Rohan-Gupta99/PrakritiNetX/assets/screenshots/mobile_app_pngs/WhatsApp Image 2026-09-10 at 23.43.37.jpeg

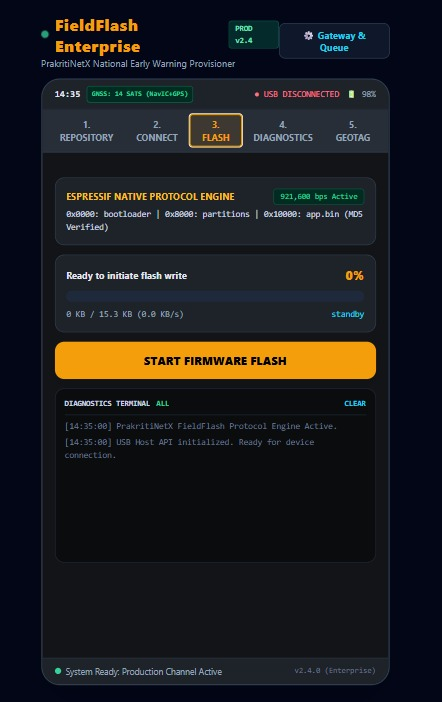
assets/screenshots/mobile_app_pngs/WhatsApp Image 2026-09-10 at 23.43.37.jpeg
