Rohan-Gupta99/PrakritiNetX/assets/screenshots/power_system_diagram.png

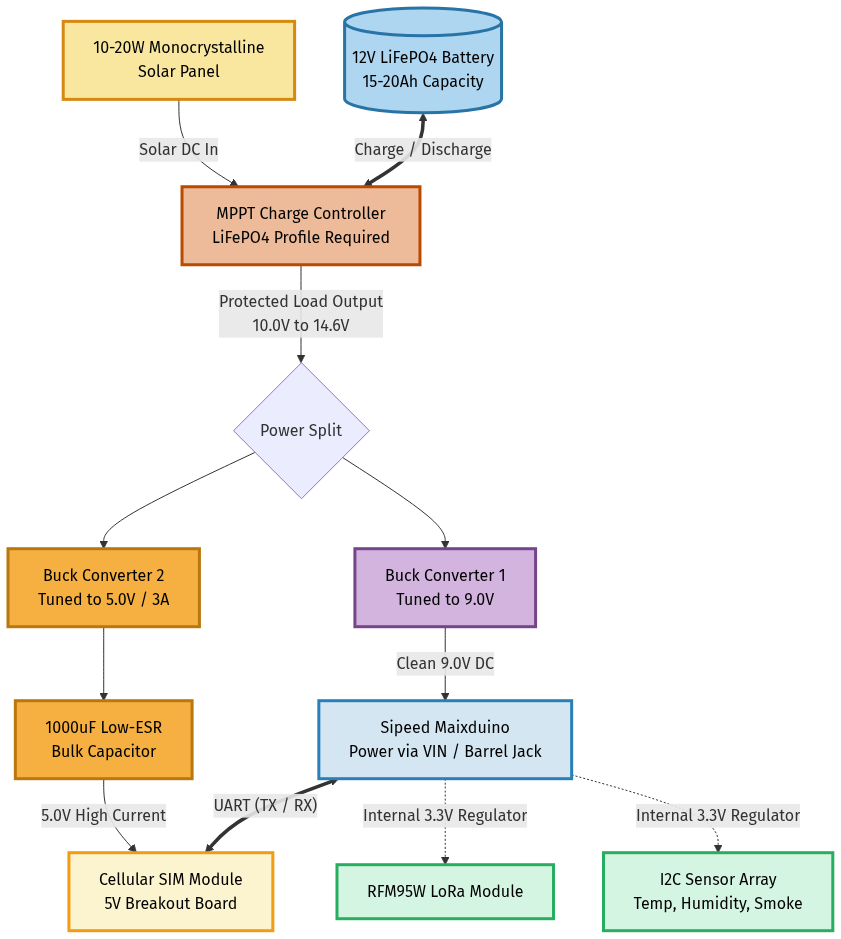
assets/screenshots/power_system_diagram.png
