Rohan-Gupta99/PrakritiNetX/Hardware/Sensor_board/Sensor_board.kicad_pcb

## KiCad design hardware/kicad/boards/01_alu/alu-32b.kicad_pcb

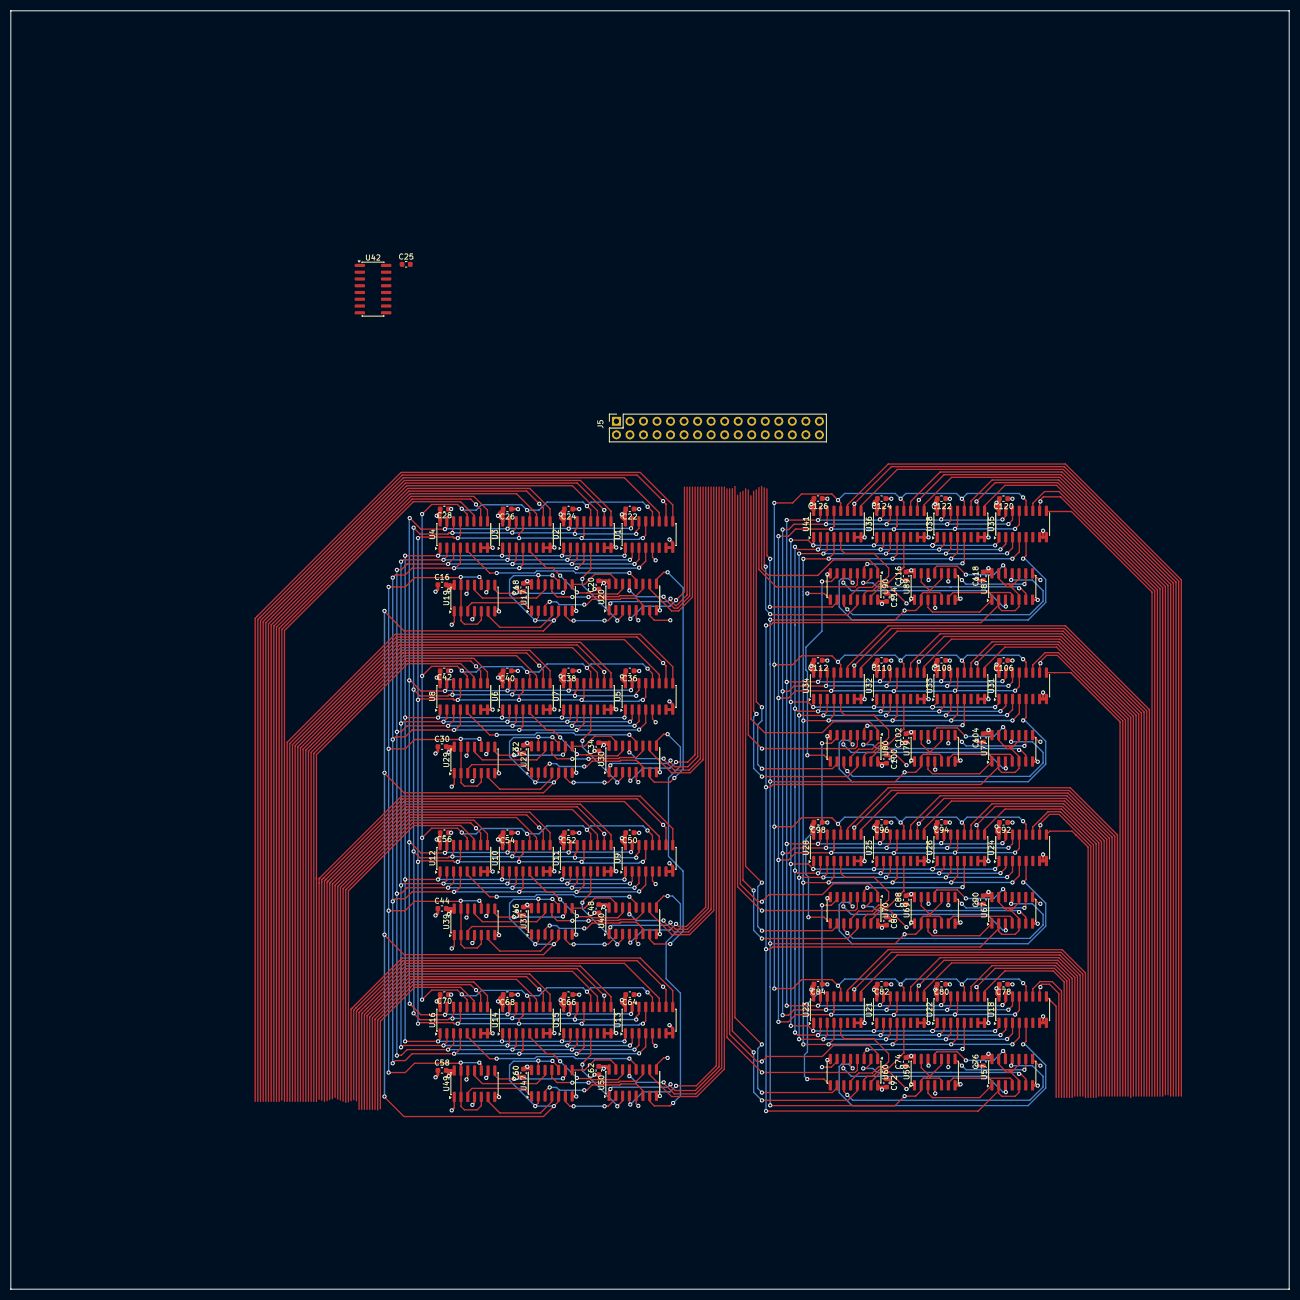
[picture p24: board alu-32b.kicad_pcb from above]

Board: 4 copper layers, 240.0 x 240.0 mm, 115 parts (0 on the bottom side), 179 nets.

Parts:
C16, C18, C20, C22, C24, C25, C26, C28, C30, C32, C34, C36, C38, C40, C42, C44, C46, C48, C50, C52, C54, C56, C58, C60, C62, C64, C66, C68, C70, C72, C74, C76, C78, C80, C82, C84, C86, C88, C90, C92, C94, C96, C98, C100, C102, C104, C106, C108, C110, C112, C114, C116, C118, C120, C122, C124, C126: 100nF; C_0603_1608Metric
J5: Conn_02x16_Counter_Clockwise; PinSocket_2x16_P2.54mm_Vertical
U1, U2, U3, U4, U5, U6, U7, U8, U9, U10, U11, U12, U13, U14, U15, U16, U18, U21, U22, U23, U24, U25, U26, U28, U31, U32, U33, U34, U35, U36, U38, U41, U42: 74ACT151; SOIC-16_3.9x9.9mm_P1.27mm
U17, U27, U37, U47, U57, U67, U77, U87: 74HC86; SOIC-14_3.9x8.7mm_P1.27mm
U19, U29, U39, U49, U59, U69, U79, U89: 74HC00; SOIC-14_3.9x8.7mm_P1.27mm
U20, U30, U40, U50, U60, U70, U80, U90: 74ACT283; SOIC-16_3.9x9.9mm_P1.27mm

Connections:
/alu-4b-0/log0: U1.5 (Z), U20.5 (A1)
/alu-4b-0/log1: U2.5 (Z), U20.3 (A2)
/alu-4b-0/log2: U3.5 (Z), U20.14 (A3)
/alu-4b-0/log3: U4.5 (Z), U20.12 (A4)
/alu-4b-0/sB0: U17.3, U20.6 (B1)
/alu-4b-0/sB1: U17.6, U20.2 (B2)
/alu-4b-0/sB2: U17.8, U20.15 (B3)
/alu-4b-0/sB3: U17.11, U20.11 (B4)
/alu-4b-1/log0: U5.5 (Z), U30.5 (A1)
/alu-4b-1/log1: U7.5 (Z), U30.3 (A2)
/alu-4b-1/log2: U6.5 (Z), U30.14 (A3)
/alu-4b-1/log3: U8.5 (Z), U30.12 (A4)
/alu-4b-1/sB0: U27.3, U30.6 (B1)
/alu-4b-1/sB1: U27.6, U30.2 (B2)
/alu-4b-1/sB2: U27.8, U30.15 (B3)
/alu-4b-1/sB3: U27.11, U30.11 (B4)
/alu-4b-2/log0: U9.5 (Z), U40.5 (A1)
/alu-4b-2/log1: U11.5 (Z), U40.3 (A2)
/alu-4b-2/log2: U10.5 (Z), U40.14 (A3)
/alu-4b-2/log3: U12.5 (Z), U40.12 (A4)
/alu-4b-2/sB0: U37.3, U40.6 (B1)
/alu-4b-2/sB1: U37.6, U40.2 (B2)
/alu-4b-2/sB2: U37.8, U40.15 (B3)
/alu-4b-2/sB3: U37.11, U40.11 (B4)
/alu-4b-3/log0: U13.5 (Z), U50.5 (A1)
/alu-4b-3/log1: U15.5 (Z), U50.3 (A2)
/alu-4b-3/log2: U14.5 (Z), U50.14 (A3)
/alu-4b-3/log3: U16.5 (Z), U50.12 (A4)
/alu-4b-3/sB0: U47.3, U50.6 (B1)
/alu-4b-3/sB1: U47.6, U50.2 (B2)
/alu-4b-3/sB2: U47.8, U50.15 (B3)
/alu-4b-3/sB3: U47.11, U50.11 (B4)
/alu-4b-4/log0: U18.5 (Z), U60.5 (A1)
/alu-4b-4/log1: U22.5 (Z), U60.3 (A2)
/alu-4b-4/log2: U21.5 (Z), U60.14 (A3)
/alu-4b-4/log3: U23.5 (Z), U60.12 (A4)
/alu-4b-4/sB0: U57.3, U60.6 (B1)
/alu-4b-4/sB1: U57.6, U60.2 (B2)
/alu-4b-4/sB2: U57.8, U60.15 (B3)
/alu-4b-4/sB3: U57.11, U60.11 (B4)
/alu-4b-5/log0: U24.5 (Z), U70.5 (A1)
/alu-4b-5/log1: U26.5 (Z), U70.3 (A2)
/alu-4b-5/log2: U25.5 (Z), U70.14 (A3)
/alu-4b-5/log3: U28.5 (Z), U70.12 (A4)
/alu-4b-5/sB0: U67.3, U70.6 (B1)
/alu-4b-5/sB1: U67.6, U70.2 (B2)
/alu-4b-5/sB2: U67.8, U70.15 (B3)
/alu-4b-5/sB3: U67.11, U70.11 (B4)
/alu-4b-6/log0: U31.5 (Z), U80.5 (A1)
/alu-4b-6/log1: U33.5 (Z), U80.3 (A2)
/alu-4b-6/log2: U32.5 (Z), U80.14 (A3)
/alu-4b-6/log3: U34.5 (Z), U80.12 (A4)
/alu-4b-6/sB0: U77.3, U80.6 (B1)
/alu-4b-6/sB1: U77.6, U80.2 (B2)
/alu-4b-6/sB2: U77.8, U80.15 (B3)
/alu-4b-6/sB3: U77.11, U80.11 (B4)
/alu-4b-7/log0: U35.5 (Z), U90.5 (A1)
/alu-4b-7/log1: U38.5 (Z), U90.3 (A2)
/alu-4b-7/log2: U36.5 (Z), U90.14 (A3)
/alu-4b-7/sB0: U87.3, U90.6 (B1)
/alu-4b-7/sB1: U87.6, U90.2 (B2)
/alu-4b-7/sB2: U87.8, U90.15 (B3)
/cout0: U20.9 (C4), U30.7 (C0)
/cout1: U30.9 (C4), U40.7 (C0)
/cout2: U40.9 (C4), U50.7 (C0)
/cout3: U50.9 (C4), U60.7 (C0)
/cout4: U60.9 (C4), U70.7 (C0)
/cout5: U70.9 (C4), U80.7 (C0)
/cout6: U80.9 (C4), U90.7 (C0)
AEFF31: U41.5 (Z), U90.12 (A4)
ALU-OPCODE0: U1.4 (I0), U2.4 (I0), U3.4 (I0), U4.4 (I0), U5.4 (I0), U6.4 (I0), U7.4 (I0), U8.4 (I0), U9.4 (I0), U10.4 (I0), U11.4 (I0), U12.4 (I0), U13.4 (I0), U14.4 (I0), U15.4 (I0), U16.4 (I0), U18.4 (I0), U21.4 (I0), U22.4 (I0), U23.4 (I0), U24.4 (I0), U25.4 (I0), U26.4 (I0), U28.4 (I0), U31.4 (I0), U32.4 (I0), U33.4 (I0), U34.4 (I0), U35.4 (I0), U36.4 (I0), U38.4 (I0), U41.4 (I0)
ALU-OPCODE1: U1.3 (I1), U2.3 (I1), U3.3 (I1), U4.3 (I1), U5.3 (I1), U6.3 (I1), U7.3 (I1), U8.3 (I1), U9.3 (I1), U10.3 (I1), U11.3 (I1), U12.3 (I1), U13.3 (I1), U14.3 (I1), U15.3 (I1), U16.3 (I1), U18.3 (I1), U21.3 (I1), U22.3 (I1), U23.3 (I1), U24.3 (I1), U25.3 (I1), U26.3 (I1), U28.3 (I1), U31.3 (I1), U32.3 (I1), U33.3 (I1), U34.3 (I1), U35.3 (I1), U36.3 (I1), U38.3 (I1), U41.3 (I1)
ALU-OPCODE2: U1.2 (I2), U2.2 (I2), U3.2 (I2), U4.2 (I2), U5.2 (I2), U6.2 (I2), U7.2 (I2), U8.2 (I2), U9.2 (I2), U10.2 (I2), U11.2 (I2), U12.2 (I2), U13.2 (I2), U14.2 (I2), U15.2 (I2), U16.2 (I2), U18.2 (I2), U21.2 (I2), U22.2 (I2), U23.2 (I2), U24.2 (I2), U25.2 (I2), U26.2 (I2), U28.2 (I2), U31.2 (I2), U32.2 (I2), U33.2 (I2), U34.2 (I2), U35.2 (I2), U36.2 (I2), U38.2 (I2), U41.2 (I2)
ALU-OPCODE3: U1.1 (I3), U2.1 (I3), U3.1 (I3), U4.1 (I3), U5.1 (I3), U6.1 (I3), U7.1 (I3), U8.1 (I3), U9.1 (I3), U10.1 (I3), U11.1 (I3), U12.1 (I3), U13.1 (I3), U14.1 (I3), U15.1 (I3), U16.1 (I3), U18.1 (I3), U21.1 (I3), U22.1 (I3), U23.1 (I3), U24.1 (I3), U25.1 (I3), U26.1 (I3), U28.1 (I3), U31.1 (I3), U32.1 (I3), U33.1 (I3), U34.1 (I3), U35.1 (I3), U36.1 (I3), U38.1 (I3), U41.1 (I3)
ALU-OPCODE4: U1.15 (I4), U2.15 (I4), U3.15 (I4), U4.15 (I4), U5.15 (I4), U6.15 (I4), U7.15 (I4), U8.15 (I4), U9.15 (I4), U10.15 (I4), U11.15 (I4), U12.15 (I4), U13.15 (I4), U14.15 (I4), U15.15 (I4), U16.15 (I4), U18.15 (I4), U21.15 (I4), U22.15 (I4), U23.15 (I4), U24.15 (I4), U25.15 (I4), U26.15 (I4), U28.15 (I4), U31.15 (I4), U32.15 (I4), U33.15 (I4), U34.15 (I4), U35.15 (I4), U36.15 (I4), U38.15 (I4), U41.15 (I4)
ALU-OPCODE5: U1.14 (I5), U2.14 (I5), U3.14 (I5), U4.14 (I5), U5.14 (I5), U6.14 (I5), U7.14 (I5), U8.14 (I5), U9.14 (I5), U10.14 (I5), U11.14 (I5), U12.14 (I5), U13.14 (I5), U14.14 (I5), U15.14 (I5), U16.14 (I5), U18.14 (I5), U21.14 (I5), U22.14 (I5), U23.14 (I5), U24.14 (I5), U25.14 (I5), U26.14 (I5), U28.14 (I5), U31.14 (I5), U32.14 (I5), U33.14 (I5), U34.14 (I5), U35.14 (I5), U36.14 (I5), U38.14 (I5), U41.14 (I5)
ALU-OPCODE6: U1.13 (I6), U2.13 (I6), U3.13 (I6), U4.13 (I6), U5.13 (I6), U6.13 (I6), U7.13 (I6), U8.13 (I6), U9.13 (I6), U10.13 (I6), U11.13 (I6), U12.13 (I6), U13.13 (I6), U14.13 (I6), U15.13 (I6), U16.13 (I6), U18.13 (I6), U21.13 (I6), U22.13 (I6), U23.13 (I6), U24.13 (I6), U25.13 (I6), U26.13 (I6), U28.13 (I6), U31.13 (I6), U32.13 (I6), U33.13 (I6), U34.13 (I6), U35.13 (I6), U36.13 (I6), U38.13 (I6), U41.13 (I6)
ALU-OPCODE7: U1.12 (I7), U2.12 (I7), U3.12 (I7), U4.12 (I7), U5.12 (I7), U6.12 (I7), U7.12 (I7), U8.12 (I7), U9.12 (I7), U10.12 (I7), U11.12 (I7), U12.12 (I7), U13.12 (I7), U14.12 (I7), U15.12 (I7), U16.12 (I7), U18.12 (I7), U21.12 (I7), U22.12 (I7), U23.12 (I7), U24.12 (I7), U25.12 (I7), U26.12 (I7), U28.12 (I7), U31.12 (I7), U32.12 (I7), U33.12 (I7), U34.12 (I7), U35.12 (I7), U36.12 (I7), U38.12 (I7), U41.12 (I7)
B0: U1.10 (S1), U19.1
B1: U2.10 (S1), U19.4
B2: U3.10 (S1), U19.9
B3: U4.10 (S1), U19.12
B4: U5.10 (S1), U29.1
B5: U7.10 (S1), U29.4
B6: U6.10 (S1), U29.9
B7: U8.10 (S1), U29.12
B8: U9.10 (S1), U39.1
B9: U11.10 (S1), U39.4
B10: U10.10 (S1), U39.9
B11: U12.10 (S1), U39.12
B12: U13.10 (S1), U49.1
B13: U15.10 (S1), U49.4
B14: U14.10 (S1), U49.9
B15: U16.10 (S1), U49.12
B16: U18.10 (S1), U59.1
B17: U22.10 (S1), U59.4
B18: U21.10 (S1), U59.9
B19: U23.10 (S1), U59.12
B20: U24.10 (S1), U69.1
B21: U26.10 (S1), U69.4
B22: U25.10 (S1), U69.9
B23: U28.10 (S1), U69.12
B24: U31.10 (S1), U79.1
B25: U33.10 (S1), U79.4
B26: U32.10 (S1), U79.9
B27: U34.10 (S1), U79.12
B28: U35.10 (S1), U89.1
B29: U38.10 (S1), U89.4
B30: U36.10 (S1), U89.9
B31: U41.10 (S1), U89.12
BEFF31: U87.11, U90.11 (B4)
GND: C16.1, C18.1, C20.1, C22.1, C24.1, C25.1, C26.1, C28.1, C30.1, C32.1, C34.1, C36.1, C38.1, C40.1, C42.1, C44.1, C46.1, C48.1, C50.1, C52.1, C54.1, C56.1, C58.1, C60.1, C62.1, C64.1, C66.1, C68.1, C70.1, C72.1, C74.1, C76.1, C78.1, C80.1, C82.1, C84.1, C86.1, C88.1, C90.1, C92.1, C94.1, C96.1, C98.1, C100.1, C102.1, C104.1, C106.1, C108.1, C110.1, C112.1, C114.1, C116.1, C118.1, C120.1, C122.1, C124.1, C126.1, U1.7 (~E), U1.8 (GND), U2.7 (~E), U2.8 (GND), U3.7 (~E), U3.8 (GND), U4.7 (~E), U4.8 (GND), U5.7 (~E), U5.8 (GND), U6.7 (~E), U6.8 (GND), U7.7 (~E), U7.8 (GND), U8.7 (~E), U8.8 (GND), U9.7 (~E), U9.8 (GND), U10.7 (~E), U10.8 (GND), U11.7 (~E), U11.8 (GND), U12.7 (~E), U12.8 (GND), U13.7 (~E), U13.8 (GND), U14.7 (~E), U14.8 (GND), U15.7 (~E), U15.8 (GND), U16.7 (~E), U16.8 (GND), U17.7 (GND), U18.7 (~E), U18.8 (GND), U19.7 (GND), U20.8 (GND), U21.7 (~E), U21.8 (GND), U22.7 (~E), U22.8 (GND), U23.7 (~E), U23.8 (GND), U24.7 (~E), U24.8 (GND), U25.7 (~E), U25.8 (GND), U26.7 (~E), U26.8 (GND), U27.7 (GND), U28.7 (~E), U28.8 (GND), U29.7 (GND), U30.8 (GND), U31.7 (~E), U31.8 (GND), U32.7 (~E), U32.8 (GND), U33.7 (~E), U33.8 (GND), U34.7 (~E), U34.8 (GND), U35.7 (~E), U35.8 (GND), U36.7 (~E), U36.8 (GND), U37.7 (GND), U38.7 (~E), U38.8 (GND), U39.7 (GND), U40.8 (GND), U41.7 (~E), U41.8 (GND), U42.4 (I0), U42.7 (~E), U42.8 (GND), U47.7 (GND), U49.7 (GND), U50.8 (GND), U57.7 (GND), U59.7 (GND), U60.8 (GND), U67.7 (GND), U69.7 (GND), U70.8 (GND), U77.7 (GND), U79.7 (GND), U80.8 (GND), U87.7 (GND), U89.7 (GND), U90.8 (GND)
unnamed: U17.1, U19.3
unnamed: U17.4, U19.6
unnamed: U17.9, U19.8
unnamed: U17.12, U19.11
unnamed: U27.1, U29.3
unnamed: U27.4, U29.6
unnamed: U27.9, U29.8
unnamed: U27.12, U29.11
unnamed: U37.1, U39.3
unnamed: U37.4, U39.6
unnamed: U37.9, U39.8
unnamed: U37.12, U39.11
unnamed: U47.1, U49.3
unnamed: U47.4, U49.6
unnamed: U47.9, U49.8
unnamed: U47.12, U49.11
unnamed: U57.1, U59.3
unnamed: U57.4, U59.6
unnamed: U57.9, U59.8
unnamed: U57.12, U59.11
unnamed: U67.1, U69.3
unnamed: U67.4, U69.6
unnamed: U67.9, U69.8
unnamed: U67.12, U69.11
unnamed: U77.1, U79.3
unnamed: U77.4, U79.6
unnamed: U77.9, U79.8
unnamed: U77.12, U79.11
unnamed: U87.1, U89.3
unnamed: U87.4, U89.6
unnamed: U87.9, U89.8
unnamed: U87.12, U89.11
OUT0: J5.1, U20.4 (S1)
OUT1: J5.2, U20.1 (S2)
OUT2: J5.3, U20.13 (S3)
OUT3: J5.4, U20.10 (S4)
OUT4: J5.5, U30.4 (S1)
OUT5: J5.6, U30.1 (S2)
OUT6: J5.7, U30.13 (S3)
OUT7: J5.8, U30.10 (S4)
OUT8: J5.9, U40.4 (S1)
OUT9: J5.10, U40.1 (S2)
OUT10: J5.11, U40.13 (S3)
OUT11: J5.12, U40.10 (S4)
OUT12: J5.13, U50.4 (S1)
OUT13: J5.14, U50.1 (S2)
OUT14: J5.15, U50.13 (S3)
OUT15: J5.16, U50.10 (S4)
OUT16: J5.17, U60.4 (S1)
OUT17: J5.18, U60.1 (S2)
OUT18: J5.19, U60.13 (S3)
OUT19: J5.20, U60.10 (S4)
OUT20: J5.21, U70.4 (S1)
OUT21: J5.22, U70.1 (S2)
OUT22: J5.23, U70.13 (S3)
OUT23: J5.24, U70.10 (S4)
OUT24: J5.25, U80.4 (S1)
OUT25: J5.26, U80.1 (S2)
OUT26: J5.27, U80.13 (S3)
OUT27: J5.28, U80.10 (S4)
OUT28: J5.29, U90.4 (S1)
OUT29: J5.30, U90.1 (S2)
OUT30: J5.31, U90.13 (S3)
VCC: C16.2, C18.2, C20.2, C22.2, C24.2, C25.2, C26.2, C28.2, C30.2, C32.2, C34.2, C36.2, C38.2, C40.2, C42.2, C44.2, C46.2, C48.2, C50.2, C52.2, C54.2, C56.2, C58.2, C60.2, C62.2, C64.2, C66.2, C68.2, C70.2, C72.2, C74.2, C76.2, C78.2, C80.2, C82.2, C84.2, C86.2, C88.2, C90.2, C92.2, C94.2, C96.2, C98.2, C100.2, C102.2, C104.2, C106.2, C108.2, C110.2, C112.2, C114.2, C116.2, C118.2, C120.2, C122.2, C124.2, C126.2, U1.16 (VCC), U2.16 (VCC), U3.16 (VCC), U4.16 (VCC), U5.16 (VCC), U6.16 (VCC), U7.16 (VCC), U8.16 (VCC), U9.16 (VCC), U10.16 (VCC), U11.16 (VCC), U12.16 (VCC), U13.16 (VCC), U14.16 (VCC), U15.16 (VCC), U16.16 (VCC), U17.14 (VCC), U18.16 (VCC), U19.14 (VCC), U20.16 (VCC), U21.16 (VCC), U22.16 (VCC), U23.16 (VCC), U24.16 (VCC), U25.16 (VCC), U26.16 (VCC), U27.14 (VCC), U28.16 (VCC), U29.14 (VCC), U30.16 (VCC), U31.16 (VCC), U32.16 (VCC), U33.16 (VCC), U34.16 (VCC), U35.16 (VCC), U36.16 (VCC), U37.14 (VCC), U38.16 (VCC), U39.14 (VCC), U40.16 (VCC), U41.16 (VCC), U42.3 (I1), U42.16 (VCC), U47.14 (VCC), U49.14 (VCC), U50.16 (VCC), U57.14 (VCC), U59.14 (VCC), U60.16 (VCC), U67.14 (VCC), U69.14 (VCC), U70.16 (VCC), U77.14 (VCC), U79.14 (VCC), U80.16 (VCC), U87.14 (VCC), U89.14 (VCC), U90.16 (VCC)
binv: U17.2, U17.5, U17.10, U17.13, U27.2, U27.5, U27.10, U27.13, U37.2, U37.5, U37.10, U37.13, U47.2, U47.5, U47.10, U47.13, U57.2, U57.5, U57.10, U57.13, U67.2, U67.5, U67.10, U67.13, U77.2, U77.5, U77.10, U77.13, U87.2, U87.5, U87.10, U87.13
bsel: U19.2, U19.5, U19.10, U19.13, U29.2, U29.5, U29.10, U29.13, U39.2, U39.5, U39.10, U39.13, U49.2, U49.5, U49.10, U49.13, U59.2, U59.5, U59.10, U59.13, U69.2, U69.5, U69.10, U69.13, U79.2, U79.5, U79.10, U79.13, U89.2, U89.5, U89.10, U89.13
cin-main: U20.7 (C0), U42.5 (Z)
